sob/shopmanual.io/docs/jeep_lj/05-control-interfaces/02-switchpros-sp1200.md

---
hide:
  - toc
tags:
  - product-details
  - control-interface
  - controller
  - switchpros
---

# SwitchPros SP-1200 (RCR-Force 12) {#switchpros-sp-1200-rcr-force-12}

/// html | div.product-info

**Model:** RCR-Force 12

**Manual:** <https://www.switchpros.com/wp-content/uploads/RCR-force-12-installation-guide-REV-1.9.pdf>

**Power Source:** 150A breaker from [Firewall CONSTANT Bus][firewall-bus] (fed from AUX battery via 250A master CB + 2/0 AWG forward feed)

**Power Wire:** 2 AWG, ~2 ft (Firewall CONSTANT Bus to power module — both at firewall cluster)

**Power Module Location:** Firewall (cabin side, passenger area) — co-located with BODY PDU and Firewall CONSTANT Bus. Module is IP67 / 125°C-rated so wheel well placement is also valid, but firewall mounting minimizes total output wire length since most loads are forward/upper (~58% of outputs).

**Control Panel Location:** Center console top plate, directly behind the [Kilduff shifter][kilduff-shifter] (owner, 2026-09-25). The panel is 4.0 x 3.0 x 0.375 in. It mounts either in a 3.875 x 2.875 in bezel cutout with 0.237 in corners, or on a flat surface on its 6-32 studs.[^rcr12-mount]

**Control Cable:** Not yet ordered. The 5 ft size was picked for a firewall-to-dash run, and the run from the firewall to the console is longer. SwitchPros sells the cable in 5 ft steps from 5 to 50 ft and says to add 6 in for strain relief.[^rcr12-cable] Measure the route before ordering.

**Ground:** 4 AWG to chassis (per manufacturer spec - reference ground only, not load return)

!!! note "Load Ground Path"
    The 4 AWG controller ground is for logic/reference only. Load return current flows through individual output grounds to the [SwitchPros Ground Bus][switchpros-ground-bus] (1/0 AWG to chassis).

**IP Rating:** IP67 (both power module and control panel)

///

## Overview

**Specifications:**

- 150A total capacity on CONSTANT bus
- 17 outputs total:
  - 4 outputs @ 35A (high in-rush circuits)
  - 1 output @ 30A (high in-rush)
  - 11 outputs @ 15A (can be combined for larger loads)
  - 1 low-side driver @ 2A

## Control Panel Layout

| Button | Circuit | Draw | Details | Output Pin(s) |
| :----: | :---: | :--: | :---: | :---: |
| 1 | Roof Lights | 17.6A| 8x BD XL Sport (Linkable, single circuit) | OUTPUT-1 |
| 2 | Ditch Lights |  8A  | 2x BD LP4 Pro (Driving/Combo Pattern) | OUTPUT-2 |
| 3 | Fog Light |  6A  | 1x BD S8 10" (Amber, Wide Cornering) | OUTPUT-3 |
| 4 | Dome Lights |  2A  | 4x KC Cyclone V2 (manual + door-triggered) | OUTPUT-4 |
| 5 | Interior LEDs |  5A  | MLC-RW controller (speaker + footwell RGB) | OUTPUT-5 |
| 6 | Rock Lights |  3A  | 6x KC Cyclone V2 Lights | OUTPUT-6 |
| 7 | Chase Light |  1A  | BD RTL-S 30" (Amber chase mode) | OUTPUT-7 |
| 8 | *Spare* |  - | Freed 2026-09-24: GPS moved to [PMU OUT14][pmu-outputs] (ignition) |  OUTPUT-8 (spare) |
| 9 | *Spare* |  - |  Freed 2026-09-24: front locker moved to a [dash switch][dashboard-controls] | OUTPUT-17 (spare, low-side) |
| 10 | *Spare* |  - | Freed 2026-09-24: rear locker moved to a [dash switch][dashboard-controls] |  OUTPUT-10 (spare) |
| 11 | Compressor | 15A  | ARB Twin Compressor (see [Air System][air-system-arb-compressor-lockers]) | OUTPUT-11 |
| 12 |  Rear Work Lights |  5A  | 2x BD S1 Black (Above License Plate) | OUTPUT-12 |

**Notes:**

- **Button 4:** Dome lights have dual control - Button 4 OR the rear-seat switch via TRIGGER-1
  - Rear-seat switch (latching, closes to ground) → TRIGGER-1 → OUTPUT-4
  - Either one turns the dome lights on. There are no door switches: the Jeep has none, and it runs half doors or no doors (owner, 2026-09-24).
- **Button 7:** RTL-S amber chase function only - brake/running/work functions powered separately
- **Button 11:** OUTPUT-11 provides control signal to ARB compressor (main power is separate: CONSTANT bus → dual 60A fuses → compressor)
- **Cargo Light:** Not assigned to button - controlled by rear rocker switch via TRIGGER-2 → OUTPUT-13 (power source conflict with BODY PDU CB20 — see {{ tbd(147) }})
- Total lighting draw if all on simultaneously: 43.6A (within 150A capacity)

## Wiring Pinout

### 20-Pin Harness Connector

| Pin | Label | Color | Gauge  |  Max Load | Assigned Circuit | Load | Notes |
| :-: | :---: | :---: | :----: | :---: | --- | :--: | :---: |
|  1  | OUTPUT-5  | GREEN | 14 AWG | 15A | Interior LEDs (MLC-RW controller)  |  5A  | |
|  2  | OUTPUT-6  | BLUE | 14 AWG | 15A | Rock Lights |  3A  | |
|  3  | IGNITION  | LT BLUE | - | - | Connect to ignition signal |  - | For auto-off features |
|  4  |  LIGHTS | WHITE | - | - | PMU Out 12 parking/tail circuit (tap at firewall) |  - | Parking-light sense — see [DRL & Parking][drl-parking] |
|  5  | OUTPUT-7  | PURPLE | 14 AWG | 15A | Chase Light (amber) |  1A  | RTL-S amber chase function only |
|  6  | OUTPUT-8  | GREY | 14 AWG | 15A | SPARE |  - | GPS moved to PMU OUT14 (2026-09-24) |
|  7  | TRIGGER-1 | PINK | - | - | Rear-seat dome switch (Blue Sea 4160) |  - | Active low; triggers OUTPUT-4 (dome lights)  |
|  8  | TRIGGER-2 | PINK | - | - | Rear cargo rocker switch |  - | Triggers OUTPUT-13 (cargo light) |
|  9  | OUTPUT-9  | WHITE | 14 AWG | 30A (2x15A) | SPARE (can combine 9+10) |  - | |
| 10  | OUTPUT-9B | WHITE | 14 AWG | - | SPARE (fused with 9) |  - | |
| 11  | OUTPUT-10 | TAN | 14 AWG | 15A | SPARE |  - | Rear locker moved to a dash switch (2026-09-24) |
| 12  | OUTPUT-11 | BROWN | 14 AWG | 15A | Compressor control | 15A  | Control signal to compressor |
| 13  | OUTPUT-12 | RED | 14 AWG | 15A | Rear Work Lights |  5A  | |
| 14  |  GROUND | BLACK | - | - | Direct to battery negative |  - | Critical - direct connection |
| 15  | OUTPUT-13 | ORANGE | 14 AWG | 15A | Cargo Light |  5A  | Triggered by rear rocker switch (TRIGGER-2) |
| 16  | OUTPUT-14 | YELLOW | 14 AWG | 15A | SPARE |  - | |
| 17  | TRIGGER-3 | PINK | - | - | ARB pressure switch |  - | Auto compressor control |
| 18  | OUTPUT-17 |  LT GREEN | - | 2A | SPARE (low-side) |  - | Front locker moved to a dash switch (2026-09-24) |
| 19  | OUTPUT-15 | GREEN/BLACK | 14 AWG | 15A | SPARE |  - | |
| 20  | OUTPUT-16 | BLUE/BLACK  | 14 AWG | 15A | SPARE |  - | |

### 4-Pin Harness (High Current Outputs)

| Pin |  Label | Color  | Gauge | Max Load | Assigned Circuit | Load | Notes |
| :-: | :---: | :----: | :---: | :---: | --- | :--: | :---: |
|  1  | OUTPUT-1 | BROWN  | 10AWG | 35A | Roof Lights (8x) | 17.6A| |
|  2  | OUTPUT-2 |  RED | 10AWG | 35A | Ditch Lights |  8A  | |
|  3  | OUTPUT-3 | ORANGE | 10AWG | 35A | Fog Light |  6A  | |
|  4  | OUTPUT-4 | YELLOW | 10AWG | 35A | Dome Lights |  2A  | |

## Power and Ground Connections

See [AUX Battery Distribution][aux-battery] for source battery and [Firewall CONSTANT Bus][firewall-bus] for downstream distribution.

- **Power:** AUX battery+ → 250A master CB → 2/0 AWG forward (~13 ft) → Firewall CONSTANT Bus → 150A CB → SwitchPros power module
- **Ground (logic reference):** 4 AWG wire from SwitchPros power module → chassis ground at firewall (short run, per manufacturer spec)
- **Load returns:** Each output's ground wire returns to the [SwitchPros Ground Bus][switchpros-ground-bus] (Blue Sea 2105 MaxiBus), co-located with the power module at the firewall

## Trigger Input Assignments

### TRIGGER-1: Rear-Seat Switch → Dome Lights

**Switch Type:** Blue Sea 4160 latching push button, used as a signal switch. It closes TRIGGER-1 to ground and carries no lamp current.

**Why not door switches:** the Jeep has no door switches and runs half doors or no doors (owner, 2026-09-24).

**Wiring:**

```text
Rear-seat switch (latching, SPST) → TRIGGER-1 (Pin 7, PINK)
Other side of switch → chassis ground
```

**Wire Routing:** Rear-seat switch location ({{ tbd(77) }}) → cabin → firewall SwitchPros. 18 AWG (signal only).

**Configuration:**

- Set TRIGGER-1 to active low in the app. The RCR-Force 12 triggers can be set to active high or active low.[^rcr12-trigger]
- Program TRIGGER-1 → OUTPUT-4. Button 4 still switches OUTPUT-4 by hand.

This replaces the parallel, CONSTANT-fed override that would have backfed OUTPUT-4. See [Dome Lights][dome-lights].

### TRIGGER-2: Rear Rocker Switch → Cargo Light

Physical rocker switch mounted in rear cargo area.

**Wiring:**

```text
Rear Cargo Rocker Switch (SPST) → TRIGGER-2 (Pin 8, PINK)
```

**Configuration:**

- Program TRIGGER-2 → OUTPUT-13 (cargo light)
- Switch type: SPST rocker or toggle switch

### TRIGGER-3: Air Pressure Switch → Auto Compressor Control

ARB air tank pressure switch automatically activates compressor to maintain tank pressure between 135-150 PSI.

**Wiring:**

```text
ARB Pressure Switch (180901) → TRIGGER-3 (Pin 17, PINK)
```

**Configuration:**

Program TRIGGER-3 to activate compressor when tank pressure drops below 135 PSI:

**SwitchPros Logic:**

- **TRIGGER-3 OR Button 11 → OUTPUT-11 (compressor)**
- When tank pressure < 135 PSI: TRIGGER-3 closes → OUTPUT-11 activates → compressor runs
- When tank pressure = 150 PSI: TRIGGER-3 opens → OUTPUT-11 deactivates → compressor stops
- Manual override: Button 11 can force compressor on regardless of tank pressure

**Signal Source:**

- ARB Pressure Switch model 180901 (cut-in: 135 PSI, cut-out: 150 PSI)
- Mounted on air manifold under passenger seat
- Low current signal wire (18 AWG from manifold under passenger seat to SwitchPros TRIGGER-3 at firewall — short run)

**Related Documentation:**

- See [Air System][air-system-arb-compressor-lockers] for complete ARB compressor, tank, and pressure switch specifications

## Outstanding Items

{{ tbds() }}

## Build Tasks

Check-off items only. Pin assignments and wire gauges live in the
[Wiring Pinout](#wiring-pinout) section above; controller mounting, power feed,
and ground bus install are tracked in the [Power Systems Checklist][power-checklist].

**Triggers & Programming:**

- [ ] Confirm ignition signal → SwitchPros Pin 3 (IGNITION)
- [x] ~~Determine parking-lights signal source for Pin 4 (LIGHTS)~~ → **Resolved 2026-09-22:** PMU Out 12 parking/tail circuit, tapped at the firewall
- [ ] Measure the control cable route (power module on the firewall to the console) and order the cable
- [ ] Install rear-seat dome switch → TRIGGER-1 (active low)
- [ ] Program Button 4: OUTPUT-4 OR TRIGGER-1 → dome lights
- [ ] Install rear cargo rocker switch → TRIGGER-2 (determine tailgate-accessible location)
- [ ] Program TRIGGER-2 → OUTPUT-13 (cargo light)
- [ ] Confirm cargo light wiring (OUTPUT-13) — power-source conflict pending {{ tbd(147) }}
- [ ] Confirm ARB pressure switch → TRIGGER-3
- [ ] Program TRIGGER-3 OR Button 11 → OUTPUT-11 (compressor auto/manual)
- [ ] Test automatic pressure control (compressor on/off at setpoints)
- [ ] Assign spare outputs: OUTPUT-8, 9, 10, 14, 15, 16 and low-side OUTPUT-17 (buttons 8, 9, 10 are free)

## Related Documentation

- [Control Interfaces Overview][control-interfaces-overview] - Main control interfaces overview
- [Offroad Lighting][offroad-auxiliary-lighting] - Complete wiring details for all lighting circuits controlled by SwitchPros
- [Air System][air-system-arb-compressor-lockers] - ARB compressor wiring details (the lockers now run from [dash switches][dashboard-controls])
- [AUX Battery Distribution][aux-battery] - Power feed specifications for SwitchPros

[aux-battery]: ../01-power-systems/03-aux-battery-distribution/index.md
[firewall-bus]: ../01-power-systems/03-aux-battery-distribution/02-constant-bus.md
[air-system-arb-compressor-lockers]: ../08-exterior-systems/02-air-compressor.md
[control-interfaces-overview]: 01-overview.md
[offroad-auxiliary-lighting]: ../04-offroad-lighting/index.md
[switchpros-ground-bus]: ../01-power-systems/05-grounding/03-switchpros-ground-bus.md
[power-checklist]: ../09-installation/01-power-systems-checklist.md
[drl-parking]: ../03-lighting-systems/05-drl-parking.md
[pmu-outputs]: ../01-power-systems/04-pmu/03-pmu-outputs.md
[dashboard-controls]: 05-dashboard-controls.md
[dome-lights]: ../03-lighting-systems/06-dome-lights.md
[kilduff-shifter]: ../10-drivetrain/01-transmission.md#shifter

[^rcr12-trigger]: SwitchPros RCR-Force 12 installation guide (Rev 1.9), pp. 4 and 7: trigger inputs "can be programmed to trigger on an active high (>4.5V) or active low" signal. <https://www.switchpros.com/wp-content/uploads/RCR-force-12-installation-guide-REV-1.9.pdf> (accessed 2026-09-24).
[^rcr12-mount]: SwitchPros RCR-Force 12 installation guide (Rev 1.9), p. 9 (flat-surface mount on the 6-32 studs, or a 3.875" x 2.875" bezel opening with a 0.237" corner radius) and p. 14 (switch panel size: width 3.0", length 4.0", height 0.375"). <https://www.switchpros.com/wp-content/uploads/RCR-force-12-installation-guide-REV-1.9.pdf> (accessed 2026-09-25).
[^rcr12-cable]: SwitchPros, "RCR-Force 12 Twelve Switch Remote Panel System" store page: cable lengths 5' to 50' in 5' steps, "add a 6 inch allowance for strain relief". <https://store.switchpros.com/rcr-force-12-twelve-switch-remote-panel-system/> (accessed 2026-09-25).
