sob/shopmanual.io/docs/jeep_lj/01-power-systems/STANDARDS-EXCEPTIONS.md

# 1.9 Standards Exceptions & Design Decisions {#standards-exceptions}

This document tracks intentional deviations from general electrical standards where manufacturer specifications, automotive practice, or engineering analysis support alternative approaches.

**Purpose:** Prevent future reviews (AI or human) from flagging intentional design decisions as oversights or errors.

---

## Winch Circuit - No External Overcurrent Protection

**Component:** WARN ZEON 10-S Winch

**Decision:** No external circuit breaker or fuse

**Standards Context:** ABYC E-11 (marine) would require CB, SAE J1128 (automotive) defers to manufacturer

### Manufacturer Specification

**WARN Installation Manual explicitly states:** "No external fuse or circuit breaker required"

- Winch includes integrated thermal protection
- Designed for direct battery connection
- Contactor provides disconnect capability

**Product Page:** [WARN ZEON 10-S][warn-product]

**Installation Manual:** [WARN Installation Guide][warn-manual]

### Winch Engineering Analysis

**Load Characteristics:**

- Typical: 250A continuous during recovery
- Peak: 409A brief (winch stall or heavy load)
- Duration: 10-30 seconds typical, 60 seconds maximum
- Duty Cycle: Brief intermittent use (not continuous)

**Wire Sizing:**

- Wire: 1/0 AWG copper (325A continuous rating @ 60°C)
- Distance: 13 ft one-way (26 ft total circuit)
- Voltage drop @ 250A: 5.32% (0.638V) - acceptable for brief accessory loads
- Voltage drop @ 409A: 8.70% (1.044V) - acceptable for brief peak loads

**Protection Mechanisms:**

1. **Internal Thermal Cutoff**
   - Winch motor has integrated thermal protection
   - Trips before windings reach damage temperature
   - Automatic reset when motor cools

2. **Contactor Disconnect**
   - Isolates winch when not in use
   - Prevents parasitic drain
   - Manual control provides emergency stop

3. **Cable Self-Protection**
   - 1/0 AWG fuses open at ~800A+ (thermal runaway)
   - Well above 409A operating peak
   - Adequate for brief loads per SAE J1128

4. **Manual Battery Disconnect**
   - Master disconnect at AUX battery terminal
   - Emergency shutoff capability
   - Maintenance safety

### Winch Standards Comparison

**Marine (ABYC E-11)** would require a 400A circuit breaker for all loads — **this is not a marine application**, so SAE J1128 (automotive) applies instead, deferring to the manufacturer spec above.

### Winch Fault Scenarios Covered

**Motor Stall (Extended Load):**

- Internal thermal cutoff trips within 60-90 seconds
- Prevents motor damage and fire hazard
- Automatic protection without user intervention

**Cable Short to Chassis:**

- 1/0 AWG cable acts as self-fusing element
- Fault current >800A required to fuse cable open
- Short circuit current path through battery ground and chassis
- Adequate protection for brief fault duration

**Contactor Weld (Stuck Closed):**

- Manual battery disconnect provides emergency stop
- Winch will run until battery depletes or thermal cutoff trips
- User can isolate at battery terminal

**Normal Operating Conditions:**

- 250-409A loads are within winch design parameters
- Cable sizing adequate per voltage drop analysis
- No fire hazard during normal recovery operations

### Winch Review Guidance

**This is NOT an oversight or safety issue** — see Manufacturer Specification, Engineering Analysis, and Standards Comparison above. **Do NOT flag as requiring correction in future reviews.**

**Documentation References:**

- [AUX Battery Distribution][aux-battery-distribution] - Winch connection details (line 37-75)
- [Recovery Systems][recovery-systems] - Complete winch specifications
- [Wire Distance Reference][wire-distance] - Winch cable routing distance

---

## Starter Circuit - No External Circuit Breaker

**Component:** Cummins R2.8 Starter Motor (factory unit shipped with the crate engine)

**Decision:** No external circuit breaker (cable sizing as protection)

**Note:** Timer relay or slow-blow CB could be added for stuck solenoid protection (optional enhancement)

### Starter Industry Standard

**Automotive Practice:**

- Starter circuits typically use cable sizing as protection
- Brief cranking duration (2-5 seconds) does not require CB
- Factory vehicles rarely include starter circuit breakers

**Cummins R2.8:**

- Starter current: 400-600A peak during cranking
- Duration: 2-5 seconds normal cranking
- No external CB specified in installation manual

### Starter Engineering Analysis

**Load Characteristics:**

- Peak: 400-600A during cranking
- Duration: 2-5 seconds typical, 10 seconds maximum recommended
- Duty Cycle: Brief intermittent (engine start only)

**Wire Sizing:**

- Wire: 2/0 AWG copper (375A continuous rating @ 60°C)
- Distance: 6 ft one-way (12 ft total circuit)
- Voltage drop @ 400A: 3.75% (0.450V) - adequate for brief cranking
- Voltage drop @ 600A: 5.61% (0.673V) - adequate for brief cranking

**Protection Strategy:**

1. **Cable Self-Protection (Brief Loads)**
   - 2/0 AWG adequate for 400-600A brief peaks
   - Thermal time constant >> cranking duration
   - No fire hazard during normal cranking

2. **Brake + START Button + P/N Interlock**
   - Prevents starter engagement unless brake pressed, START button held, and shifter in P or N
   - Triple gate eliminates accidental cranking and in-gear cranking

3. **Two-Stage Relay Control**
   - Cole Hersee 24213 solenoid controls high current
   - Low-current control circuit provides isolation

### Potential Fault Scenario: Stuck Solenoid

**Risk:**

- Starter solenoid welds closed or jams
- 400-600A sustained until battery depletes
- Cable heating, potential fire hazard

**Mitigation Options:**

#### Option 1: Timer Relay (Recommended)

- Install 10-second timer in Cole Hersee control circuit
- Cuts power after 10 seconds continuous cranking
- Prevents starter damage and cable overheating
- Lower cost than 500A circuit breaker
- **Status:** Recommended enhancement, not critical requirement

#### Option 2: 500A Slow-Blow Circuit Breaker

- Allows brief 600A cranking peaks
- Trips on sustained high current
- Mechanical Products Series 17 available
- **Status:** Alternative to timer relay

#### Option 3: Current Design (Cable Protection Only)

- Adequate for brief normal cranking ✓
- Relies on user awareness for stuck solenoid
- Manual battery disconnect available
- **Status:** Acceptable per automotive practice, enhancement recommended

### Starter Standards Comparison

**Marine (ABYC E-11)** would require a circuit breaker or fuse — **this is not a marine application**, so SAE J1128 (automotive) applies instead, per the practice and analysis above.

### Starter Review Guidance

**Current design (no CB) is acceptable per automotive standards — do NOT flag as a critical safety issue.** Timer relay remains a recommended (not critical) enhancement; see Option 1 above.

**Documentation References:**

- [Starter System][starter-system] - Complete starter specifications and wiring (line 1-125)
- [START Battery Distribution][starter-battery-distribution] - Starter power connection (line 37)

---

## Grid Heater - Direct Battery Connection (No CB)

**Component:** Cummins R2.8 Grid Heater Relay (Part# 5467024)

**Decision:** Direct battery connection with fusible link (no circuit breaker)

### Grid Heater Manufacturer Specification

**Cummins Installation:**

- ECM controls grid heater relay directly
- High current (40-80A) for brief duration (3-5 seconds)
- Direct battery connection specified
- Fusible link protection integrated

### Grid Heater Engineering Analysis

**Load Characteristics:**

- Current: 40-80A during cold start aid
- Duration: 3-5 seconds (brief pulse)
- Duty Cycle: Only during cold starts (<50°F ambient)
- Frequency: Infrequent (cold weather only)

**Protection Strategy:**

- Integrated fusible link in relay assembly
- ECM manages duty cycle and temperature thresholds
- Brief duration eliminates thermal concerns
- Direct connection minimizes voltage drop for effective heating

### Grid Heater Review Guidance

**This is intentional per manufacturer specifications** — see Engineering Analysis above. **Do NOT flag as requiring circuit breaker.**

**Documentation References:**

- [Grid Heater System][grid-heater] - Complete grid heater specifications

---

## Alternator Output - No Circuit Breaker

**Component:** Premier Power Welder HO-C28 270A Alternator

**Decision:** No circuit breaker between alternator and battery

### Alternator Industry Standard

**All automotive alternators connect directly to battery without circuit breaker:**

- Factory vehicle practice: No CB on alternator output
- Alternator has internal voltage regulation
- Charging circuit protected by battery capacity and cable sizing

### Alternator Engineering Analysis

**Why No Circuit Breaker Required:**

1. **Alternator Self-Limiting**
   - Maximum output: 270A (design limit)
   - Cannot exceed rated output regardless of load
   - Internal voltage regulator prevents overcharge

2. **Cable Sizing**
   - Wire: 2/0 AWG (375A continuous rating)
   - Adequate for 270A continuous output
   - No thermal concerns at rated load

3. **Battery Acts as Buffer**
   - Absorbs brief load spikes
   - Prevents alternator overload
   - Natural load smoothing

### Alternator Review Guidance

**This is standard automotive practice** — see Industry Standard and Engineering Analysis above. **Do NOT flag as missing protection.**

**Documentation References:**

- [Alternator][alternator] - Alternator specifications and output connection

---

## BCDC Charging Input - No Dedicated Circuit Breaker

**Component:** RedArc BCDC Alpha 50 DC-DC Charger

**Decision:** 80A circuit breaker at START battery terminal (not at BCDC)

### BCDC Manufacturer Specification

**RedArc Installation:**

- Circuit breaker required within 7" of battery positive
- No requirement for CB at BCDC input
- 80A CB adequate for 50A charging current + inrush

### BCDC Engineering Analysis

**Protection Location:**

- CB at battery terminal (compliant with 7" requirement) ✓
- Protects entire cable run from battery to BCDC ✓
- No additional CB needed at BCDC end

**Load Characteristics:**

- Normal: 50A DC-DC charging
- Peak: 50-55A (manufacturer spec)
- 80A CB sized at 145-160% of max load (appropriate margin)

### BCDC Review Guidance

**Circuit breaker at the battery terminal is the correct protection point** — see Engineering Analysis above. **Do NOT flag as missing protection at BCDC.**

**Documentation References:**

- [BCDC Alpha 50][bcdc] - BCDC installation and protection requirements
- [START Battery Circuit Breakers][starter-cbs] - 80A CB specification

---

## START+ Forward Distribution Bus - Bus Bar Between Battery and Loads

**Components:** START+ Forward Distribution Bus (engine bay) feeding the relocated radiator fan, iBooster, and TCU

**Decision:** A single 100A master-protected 2 AWG feed runs from the START battery to an engine-bay busbar that fans out to three load breakers — a deliberate departure from the START-side "direct lugs, no bus bar between battery and loads" principle.

### Engineering Rationale

- The radiator fan, iBooster, and TCU were moved off the PMU and all sit forward (engine bay / transmission), while the START battery is in the rear wheel well.
- Three independent feeds would mean three long rear-to-front cables and ~9 stacked lugs on the battery post (impractical, hard to service).
- A single master feed + forward busbar mirrors the proven AUX-side two-stage architecture (250A master → firewall CONSTANT bus), placing each load's breaker near its load.
- The intermediate bus is a passive bar; the feed is protected by a 100A master breaker within 7" of the battery (the cable is never unprotected), with selective coordination to the downstream load breakers.

### Review Guidance

**This is intentional.** Do NOT flag the START+ Forward Distribution Bus as violating the "no bus bar between battery and loads" rule — it is the same accepted tradeoff as the AUX CONSTANT bus, chosen to relocate three critical loads off the PMU. See {{ tbd(135) }} for final busbar/breaker selection.

**Documentation References:**

- [START Battery Distribution][starter-battery-distribution] - Forward bus feed and load table
- [START Battery Circuit Breakers][starter-cbs] - Master + load breakers

---

## SwitchPros & SafetyHub - CB Sized for Device Capacity

**Components:** SwitchPros RCR-Force 12, Blue Sea SafetyHub 150

**Decision:** 150A circuit breakers protecting 2 AWG wire (130A @ 20°C)

**Apparent Issue:** CB rating (150A) exceeds wire continuous ampacity (130A) by 15%

### Engineering Analysis

**Why This Is Safe:**

The CB is sized for _device capacity_, not actual load. Actual loads are well within wire rating:

| Device | Device Max | Actual Load | Wire Rating | Load % of Wire |
| :--- | :--- | :--- | :--- | :--- |
| SwitchPros | 150A | ~48A | 130A | 37% |
| SafetyHub  | 150A | 100A | 130A | 77% |

**SwitchPros Actual Load Breakdown:**

- Roof lights: 18A (8x XL Sport @ 2.2A each)
- Auxiliary lights: 26A (ditch 8A, fog 6A, work 5A, rock 3A, dome 2A, chase 1A, rear 5A)
- Lockers: 4A
- **Total: ~48A** (32% of CB rating)

**SafetyHub Actual Load Breakdown:**

- ARB Compressor: 90A (2x 45A motors)
- Winch trigger: 10A
- **Total: 100A** (67% of CB rating)

### Protection Strategy

**Normal Operation:**

- Wire operates at 37-77% of its ampacity
- No thermal stress, adequate safety margin
- Wire temperature remains well below insulation rating

**Fault Condition (Short Circuit):**

- Fault current exceeds CB rating → CB trips
- Brief overload duration (milliseconds to seconds) insufficient to damage wire
- 2 AWG thermal mass absorbs brief fault current safely

**CB Trip Curve Analysis:**

- Mechanical Products Series 17 trips at 135% of rating within 30 seconds
- At 150A × 135% = 202A, CB trips before wire reaches damage temperature
- Short circuit currents (500A+) trip CB nearly instantaneously

### Wire Sizing Rationale

**Why 2 AWG (not 1/0 AWG):**

1. **Actual load headroom:** 82-100A loads have 30-48A margin to wire rating
2. **Consistency:** All CONSTANT bus outputs use 2 AWG for standardization
3. **Future flexibility:** 130A wire supports load growth within device capacity
4. **Cost/weight:** 1/0 AWG unnecessary for actual loads

**Why 150A CB (not 125A):**

1. **Device protection:** Matches SwitchPros and SafetyHub rated capacity
2. **Inrush tolerance:** Lighting loads have brief inrush spikes
3. **Future headroom:** Allows adding loads up to device capacity

### Standards Context

**ABYC E-11 (Marine):**

- Requires CB ≤ wire ampacity for continuous loads
- **However:** Actual loads are not continuous at full capacity
- SwitchPros lighting loads are intermittent (not 24/7 operation)
- SafetyHub ARB compressor runs only during airing up (minutes, not hours)

**SAE J1128 (Automotive):**

- Wire sizing based on actual load, not theoretical maximum
- CB sizing considers duty cycle and thermal time constants
- Brief overloads acceptable if within wire thermal limits

### Review Guidance

**This is NOT a safety issue** — the apparent CB > wire mismatch is intentional; see Engineering Analysis, Wire Sizing Rationale, and Standards Context above. **Do NOT flag as requiring wire upgrade or CB downgrade.**

**Documentation References:**

- [AUX Battery Circuit Breakers][aux-cbs] - CB specifications
- [CONSTANT Bus Bar][constant-bus] - Wire specifications
- [SwitchPros][switchpros] - Load assignments and totals
- [SafetyHub][safetyhub] - Circuit assignments and loads

---

## Summary of Intentional Design Decisions

**All decisions documented above are intentional and based on:**

1. **Manufacturer Specifications** - Following OEM installation requirements
2. **Automotive Standards (SAE J1128)** - Primary standard for automotive electrical systems
3. **Industry Practice** - Factory vehicle precedents and proven approaches
4. **Engineering Analysis** - Load characteristics, wire sizing, fault scenarios

**These are NOT oversights, errors, or safety issues.**

**Marine standards (ABYC E-11) are referenced selectively:**

- Applied to: Dual battery architecture, accessory circuits, grounding
- **NOT applied to:** Starter, alternator, winch, grid heater (automotive components)

---

## Breaker-vs-Wire Preference (2026-09-22)

Owner rule: **keep the smaller wire and drop the breaker to it.** When a review finds a breaker above its conductor's ampacity, the fix is a lower-rated breaker at or below the wire rating, not a heavier cable — the build is already carrying a lot of copper. Applied so far:

| Circuit | Was | Now | Wire it protects |
| :--- | :-- | :-- | :--- |
| START+ Forward Distribution Bus master | 150A | 100A | 2 AWG (110A @ 60°C) |
| AUX forward feed to Firewall CONSTANT Bus | 300A | 250A | 2/0 AWG (~265A @ 60°C); matches the 2105 bus rating |
| JL Audio MV800/8i amp feed | 100A | 80A | 4 AWG (95A @ 20°C); equals the amp's recommended fuse |

Manufacturer-specified breakers (SwitchPros 150A, SafetyHub 150A) keep their exception above.

## Review Checklist for Future Analysis

Before flagging as issues, verify these intentional design choices:

- [ ] **Winch:** No external CB per WARN manufacturer spec ✓
- [ ] **Starter:** Direct battery connection, cable sizing as protection (timer relay optional enhancement)
- [ ] **Grid Heater:** Direct battery connection with fusible link (brief high current)
- [ ] **Alternator:** No CB on output (standard automotive practice)
- [ ] **BCDC:** CB at battery terminal (no CB at BCDC end required)
- [ ] **START+ Forward Bus:** 100A master + forward busbar between battery and fan/iBooster/TCU (intentional, mirrors AUX CONSTANT bus)
- [ ] **SwitchPros/SafetyHub:** 150A CB with 2 AWG wire (actual loads 82-100A, within 130A wire rating)

**If any of these are flagged as "missing protection" or "safety issues" in future reviews, refer to this document for complete justification.**

---

[warn-product]: https://www.warn.com/products/zeon-10-s-89611
[warn-manual]: https://www.warn.com/products/zeon-10-s-89611
[aux-battery-distribution]: 03-aux-battery-distribution/index.md
[recovery-systems]: ../08-exterior-systems/01-winch.md
[wire-distance]: 01-power-generation/05-wire-distance-reference.md
[starter-system]: ../02-engine-systems/01-starter.md
[starter-battery-distribution]: 02-starter-battery-distribution/index.md
[grid-heater]: ../02-engine-systems/07-grid-heater.md
[alternator]: 01-power-generation/02-alternator.md
[bcdc]: 01-power-generation/03-bcdc.md
[starter-cbs]: 02-starter-battery-distribution/01-circuit-breakers.md
[aux-cbs]: 03-aux-battery-distribution/01-circuit-breakers.md
[constant-bus]: 03-aux-battery-distribution/02-constant-bus.md
[switchpros]: ../05-control-interfaces/02-switchpros-sp1200.md
[safetyhub]: 03-aux-battery-distribution/04-safetyhub.md
