sob/shopmanual.io/docs/jeep_lj/02-engine-systems/01-starter.md

---
hide:
  - toc
tags:
  - product-details
  - engine-systems
  - starter
---

# 2.1 Starter System {#starter-system-cummins-r28}

/// html | div.product-info
**Type:** 12V Diesel Starter Motor

**Model:** Cummins factory starter — shipped mounted on the R2.8 crate engine[^kit-starter]

**Status:** In hand (owner decision 2026-09-22: keep the factory unit)

**Manufacturer:** Cummins (supplier unit)

**Voltage:** 12V

**Mounting:** Engine block (as shipped)

**Power Source:** START battery+ direct connection (2/0 AWG)

**Replacement reference (not purchased):** [DB Electrical 410-52442][db-starter] — aftermarket cross-reference to Cummins 4996706 / Denso 428000-7090; useful only if the factory unit ever needs replacing.

///

[^kit-starter]: Cummins Repower R2.8 Installation Guide (Bulletin 5504137), §1 "Starter", p. 1-36: "The engine kit includes an engine mounted 12 volt starting motor." Local copy: `resources/cummins-r2.8-installation-guide.pdf`.

## System Configuration

**Control Method:** Two-stage relay system

**Main Power Source:** START battery+ direct connection (see [START Battery Distribution][starter-battery] for wire specs)

**Control Solenoid:** Cole Hersee 24213 (200A continuous-duty)[^ch-24213]

**Safety Interlock:** The crank signal (60A PURPLE START) comes solely from the PBS-I keyless module, which owns RFID authorization, the brake interlock, ACC/IGN/START sequencing, and the cold-start WAIT-to-Start lamp procedure — see [Keyless Ignition][keyless-ignition]. (An automatic crank lockout was evaluated and deferred — see the [WAIT-to-Start Lockout Design Note][wait-lockout-note].)

**Battery Requirement:** 800 CCA minimum (Odyssey PC1500 provides 850 CCA)

## Wiring

| Circuit | Source | Destination | Wire Gauge | Current  | Notes |
| :--- | :--- | :--- | :--- | :--- | :--- |
| Main Power | START battery+ | Starter solenoid battery post | 2/0 AWG | 400-600A | See [START Battery Distribution][starter-battery] for wire specs |
| Solenoid Power Tap | START battery post | Cole Hersee 24213 input | 10 AWG | 30-75A | ~2 ft |
| Start Signal | PBS-I PURPLE START output | Firewall Pin 15 → Cole Hersee coil+ | 16 AWG  | ~0.69A | PBS-I output rated 60A but only Cole Hersee coil downstream[^ch-24213] |
| Solenoid Coil Ground  | Cole Hersee 24213 coil- | Engine bay ground bus | 16 AWG | ~0.69A | ~3 ft |
| Solenoid Output | Cole Hersee 24213 output | Starter solenoid switch post | 10 AWG | 30-75A | ~2 ft |
| Ground Return | Starter case | Engine block → START battery- | 2/0 AWG | 400-600A | Via engine bay ground bus |

See [Keyless Ignition][keyless-ignition] for PBS-I power and brake input wiring.

## Control Flow

```text
PBS-I asserts PURPLE START  (fob auth + brake + sequence: see Keyless Ignition)
            ↓
PURPLE START → Firewall Pin 15 → Cole Hersee 24213 coil → Ground
            ↓
Cole Hersee main contacts close
            ↓
START battery → Cole Hersee output → Starter switch post → Bendix engages → cranks
            ↓
Engine starts → button released → Cole Hersee de-energizes → Bendix retracts
```

## Starter Motor Terminals

**Battery Post (M8 x 1.25 thread, qty 2):**

- Main power from START battery (2/0 AWG)
- Power tap for control solenoid (10 AWG)

**Switch Post (6.3mm flat male push-on):**

- Trigger from Cole Hersee 24213 output (10 AWG, 30-75A)

**Ground:**

- Via starter mounting bolts to engine block

## Cole Hersee 24213 Solenoid

**Specifications:**

- Rating: 200A continuous duty[^ch-24213]
- Coil Voltage: 12V DC
- Coil Draw: ~0.69A (17.5 Ω coil @ 12V)[^ch-24213]
- Mounting: Firewall (engine bay side)

**Terminals:**[^ch-24213]

- Large Stud 1 (Input): 5/16"-24 copper power stud; from START battery post (10 AWG)
- Large Stud 2 (Output): 5/16"-24 copper power stud; to starter switch post (10 AWG; starter post is 6.3mm push-on)
- Small Stud 1 (Coil+): #10-32 steel stud; from Firewall Pin 15 (16 AWG, PBS-I PURPLE START)
- Small Stud 2 (Coil-): #10-32 steel stud; to engine bay ground bus (16-18 AWG)

[^ch-24213]: Littelfuse (Cole Hersee) 24213 continuous-duty SPST solenoid, [product page](https://www.littelfuse.com/products/relays-contactors-transformers/solenoids-relays/standard-high-current-relays/continuous-duty-spst/24213) / DigiKey #6347082. Rated **200A continuous** with two 5/16"-24 copper power studs + two #10-32 steel coil studs; coil ~0.69A @ 12V (17.5 Ω). Corrects the earlier unsourced "85A / M8 / 6.3mm-push-on" figures (validated 2026-05-30). 200A is comfortably oversized for the ~10A starter-trigger path.

## Outstanding Items

{{ tbds() }}

## Build Tasks

- [ ] Record the factory starter's part number from its tag (the terminal posts and current figures below were taken from the aftermarket cross-reference; confirm on the unit)

[install-checklist]: ../09-installation/02-engine-systems-checklist.md

## Related Documentation

- [START battery Distribution][starter-battery-distribution] - Main power source
- [Firewall Ingress][firewall-ingress] - Ignition START wire routing
- [Engine Bay Ground Bus][engine-bay-ground-bus] - Ground connections
- [Power Generation][power-generation] - Battery specifications
- [Wire Distance Reference][wire-distance] - Starter to battery routing distances
- [Keyless Ignition][keyless-ignition] - PBS-I sources PURPLE START; cold-start wait via the WAIT-to-Start lamp
- [WAIT-to-Start Lockout Design Note][wait-lockout-note] - Deferred automatic crank-lockout design, preserved for future revival

[db-starter]: https://www.dbelectrical.com/products/starter-for-2-8-cummins-isf2-8-qsb3-9-30-qsb4-5-4996706-428000-7090.html
[starter-battery-distribution]: ../01-power-systems/02-starter-battery-distribution/index.md
[starter-battery]: ../01-power-systems/02-starter-battery-distribution/index.md
[firewall-ingress]: ../01-power-systems/07-wire-routing/02-firewall-ingress.md
[engine-bay-ground-bus]: ../01-power-systems/05-grounding/01-engine-bay-ground-bus.md
[power-generation]: ../01-power-systems/01-power-generation/index.md
[wire-distance]: ../01-power-systems/01-power-generation/05-wire-distance-reference.md
[keyless-ignition]: ../05-control-interfaces/06-keyless-ignition.md
[wait-lockout-note]: wait-to-start-lockout-design-note.md
[tbd-tracker]: ../tbd-tracker.md
