sob/shopmanual.io/docs/jeep_lj/08-exterior-systems/04-rear-air-chuck.md

---
hide:
  - toc
tags:
  - product-details
  - exterior-systems
  - air-system
---

# 8.4 Rear Air Chuck {#rear-air-chuck}

External air access plate mounted in the tailgate area for tire inflation, air tool use, and trail-side air sharing with other vehicles.

/// html | div.product-info

**Type:** Quick-disconnect air chuck plate

**Location:** Tailgate area

**Air Source:** [Air Compressor][air-compressor] via manifold (1/4" air line)

///

## Specifications

| Spec | Value |
| --- | --- |
| Connector Type | Industrial quick-disconnect (1/4" NPT) |
| Working Pressure | 150 PSI (matches tank pressure) |
| Air Line | 1/4" OD nylon tubing from manifold |
| Mounting | Flush-mount plate in tailgate area |

## Air Line Routing

**Route:** Manifold (under passenger seat) → along interior → to tailgate area

- **Line Type:** 1/4" OD nylon tubing (200 PSI rated)
- **Fittings:** Push-to-connect at manifold, NPT fitting at chuck plate
- **Protection:** Route inside vehicle where possible, protect at penetrations

## Outstanding Items

{{ tbds() }}

## Build Tasks

- [ ] Select air chuck plate model/part number
- [ ] Determine exact mounting location in tailgate area
- [ ] Measure air line length from manifold to tailgate
- [ ] Order air chuck plate and fittings

## Related Documentation

- [Air Compressor][air-compressor] - Air source and manifold
- [Air Lockers][air-lockers] - Other air system consumers

[air-compressor]: 02-air-compressor.md
[air-lockers]: 03-air-lockers.md
