sob/shopmanual.io/docs/jeep_lj/04-offroad-lighting/10-reverse-lights.md

---
hide:
  - toc
tags:
  - product-details
  - lighting
  - offroad
  - pmu-controlled
  - baja-designs
---

# 4.10 Reverse Lights {#reverse-lights}

Reverse lights (4,520 lumens combined) that activate automatically via PMU reverse circuit.

/// html | div.product-info
Baja Designs Squadron Sport

**Type:** LED Pod Light

**Model:** Squadron Sport Black - Wide Cornering

**Part Number:** 557805

**Manufacturer:** Baja Designs

**Product Page:** [Squadron Sport Wide Cornering Pair][product-link]

**Quantity:** 2 pods

**Mounting:** Rear armor brackets

**Power Source:** PMU Out 22 (automatic with reverse gear)

///

## Specifications

| Spec | Value |
| :--- | ---: |
| Beam Pattern | Wide Cornering 42° |
| Lens | Clear |
| Output | 2,260 lumens each (4,520 total) |
| Draw | 1.4A each (2.8A total) |
| IP Rating | IP69K |

## Control

**Controller:** PMU Out 22 (automatic with reverse gear)

Wired in parallel with Maxbilt Round Trail Tail WHITE (reverse) and WolfBox camera trigger.

See [Tail/Brake/Reverse Lights][tail-brake-reverse] for PMU reverse circuit details and combined load verification.

## Related Documentation

- [Offroad Lighting Overview][offroad-overview]
- [Tail/Brake/Reverse Lights][tail-brake-reverse] - PMU Out 22 reverse circuit
- [Rear Work Lights][rear-lights] - Separate SwitchPros-controlled rear lights

[offroad-overview]: index.md
[tail-brake-reverse]: ../03-lighting-systems/04-tail-brake-reverse.md
[rear-lights]: 08-rear-lights.md
[product-link]: https://www.bajadesigns.com/products/squadron-sport-led-light-557805.html
