sob/shopmanual.io/docs/jeep_lj/04-offroad-lighting/07-cargo-lights.md

---
hide:
  - toc
tags:
  - product-details
  - lighting
  - offroad
  - baja-designs
---

# 4.7 Cargo Lights {#cargo-lights}

Interior cargo area lighting controlled by physical switch (Baja Designs Zone 7).

/// html | div.product-info
Baja Designs S2 Sport Flush Mount

**Type:** LED Flush Mount Light

**Model:** S2 Sport Black Flush Mount

**Part Number:** 541006

**Manufacturer:** Baja Designs

**Product Page:** [S2 Sport Black Flush Mount][product-link]

**Quantity:** 2 pods

**Mounting:** Flush mount inset on rear wheel well (cargo area)

**Power Source:** BODY PDU (via physical switch)

///

## Specifications

| Spec | Value |
| :--- | ---: |
| Beam Pattern | Work/Scene |
| Lens | Clear |
| Draw | ~2A each (4A total) |

## Control

**Controller:** [Blue Sea 4160 Push Button Switch][switch-link]

**Switch Location:** Top of rear wheel well (accessible from tailgate)

**Wiring:** BODY PDU CB20 (10A) → Switch → Cargo lights → Ground (power-source conflict with OUTPUT-13/TRIGGER-2 open — {{ tbd(147) }})

| Spec | Value |
| :--- | ----: |
| Switch Rating | 10A @ 12V |
| Load | 4A |
| Action | OFF-ON (latching) |
| Mounting Hole | 3/4" (19mm) |

## Related Documentation

- [Offroad Lighting Overview][offroad-overview]
- [BODY PDU][body-pdu] - CB20 power source

[offroad-overview]: index.md
[body-pdu]: ../01-power-systems/03-aux-battery-distribution/03-body-pdu.md
[product-link]: https://www.bajadesigns.com/products/s2-sport-black-flush-mount-led-auxiliary-light-pod/?sku=541006
[switch-link]: https://www.bluesea.com/products/4160/10A_Push_Button_LED_Ring_Switch_OFF-ON_Blue
