sob/shopmanual.io/docs/jeep_lj/04-offroad-lighting/03-roof-lights.md

---
hide:
  - toc
tags:
  - product-details
  - lighting
  - offroad
  - switchpros-controlled
  - baja-designs
---

# 4.3 Roof Lights {#roof-lights}

Primary forward illumination mounted on roof rack (Baja Designs Zone 3 + Zone 4).

/// html | div.product-info
Baja Designs XL Sport Linkable 8-Pod

**Type:** LED Pod Light (Linkable)

**Model:** XL Sport Linkable

**Part Number:** 740006

**Manufacturer:** Baja Designs

**Product Page:** [XL Sport Linkable 8-Pod][product-link]

**Quantity:** 8 pods total

**Harness:** [XL Linkable Wiring Harness 8-Pod][harness-link] (640192)

**Mounting:** [XL Linkable Pre-Load Mount][preload-link] (748002) center + [XL Linkable Brackets][bracket-link] (748000) sides

**Power Source:** SwitchPros OUTPUT-1

///

## Wiring

All 8 pods on single circuit via XL Linkable harness.

**Wire Routing:** Passenger A-pillar from SwitchPros (engine bay) to roof rack.

**Controller:** SwitchPros Button 1 (OUTPUT-1) - 17.6A load on 35A output (50% utilization)

## Specifications

| Spec | Value |
| :--- | ---: |
| Output | 9,000 lumens each |
| Draw | 2.2A each (30.36W) |
| Total Output | 72,000 lumens |
| Total Draw | 17.6A |

See [SwitchPros SP-1200][switchpros-sp-1200] for wiring details.

## Outstanding Items

{{ tbds() }}

## Build Tasks

- [ ] Plan wire routing from SwitchPros to roof rack (passenger A-pillar to roof)
- [ ] Confirm roof rack mounting points for XL Linkable brackets

## Related Documentation

- [Offroad Lighting Overview][offroad-overview]
- [SwitchPros SP-1200][switchpros-sp-1200]

[offroad-overview]: index.md
[switchpros-sp-1200]: ../05-control-interfaces/02-switchpros-sp1200.md
[product-link]: https://www.bajadesigns.com/products/xl-sport-linkable-led-light-bar-universal/?sku=740006
[harness-link]: https://www.bajadesigns.com/products/xl-linkable-wiring-harness-universal/?sku=640192
[preload-link]: https://www.bajadesigns.com/products/xl-linkable-led-light-bar-pre-load-mount/?sku=748002
[bracket-link]: https://www.bajadesigns.com/products/xl-linkable-led-light-bar-brackets/?sku=748000
