sob/shopmanual.io/docs/jeep_lj/04-offroad-lighting/06-rock-lights.md

---
hide:
  - toc
tags:
  - product-details
  - lighting
  - offroad
  - switchpros-controlled
  - kc-hilites
---

# 4.6 Rock Lights {#rock-lights}

Underbody lighting for wheel wells and frame rails (Baja Designs Zone 6).

/// html | div.product-info
KC HiLiTES Cyclone V2

**Type:** LED Rock Light

**Model:** Cyclone V2

**Part Number:** 1352 (single light)

**Manufacturer:** KC HiLiTES

**Product Page:** [Cyclone V2][product-link]

**Quantity:** 6 pods

**Mounting:** 4 in wheel wells (one per corner), 1 front bumper, 1 rear bumper

**Power Source:** SwitchPros OUTPUT-6

///

## Specifications

| Spec | Value |
| :----- | ---: |
| Output | 200 lumens each (1,200 total) |
| Draw | 0.5A each (3A total) |
| Size | 2.4" diameter round |

## Control

**Controller:** SwitchPros Button 6 (OUTPUT-6)

See [SwitchPros SP-1200][switchpros-sp-1200] for wiring details.

**Protection:** Braided sleeving with soldered connections and marine heat shrink.

## Outstanding Items

{{ tbds() }}

## Build Tasks

- [ ] Plan wire routing from SwitchPros to wheel wells and bumpers

## Related Documentation

- [Offroad Lighting Overview][offroad-overview]
- [SwitchPros SP-1200][switchpros-sp-1200]

[offroad-overview]: index.md
[switchpros-sp-1200]: ../05-control-interfaces/02-switchpros-sp1200.md
[product-link]: https://www.kchilites.com/cyclone-v2-cyclone-v2-led-single-light.html?attr_pim_lenscolor=5730
