sob/shopmanual.io/docs/jeep_lj/01-power-systems/02-starter-battery-distribution/index.md

---
hide:
  - toc
---

# 1.2 START battery Distribution (Driver Rear Wheel Well) {#starter-battery-distribution}

/// html | div.product-info
Odyssey PC1500 Battery Terminals
///

## Overview

The START battery (driver rear wheel well) provides power for critical engine and safety systems:

1. **Direct high-current** → Starter (no CB), alternator charging input (no CB)
2. **Circuit breaker protected** → PMU (250A CB), BCDC (80A CB)
3. **[START+ Forward Distribution Bus](#start-forward-bus)** (100A master CB → single feed → engine-bay busbar) → radiator fan (60A), iBooster main (50A), TCU (25A) — relocated off the PMU
4. **Direct low-current** → ECM, grid heater (fusible link protection)

See [Circuit Breakers][circuit-breakers] for complete CB specifications. All CBs mounted in rear wheel well within 7" of battery (code compliant).

!!! info "Single Source of Truth"
This page is the authoritative source for all START battery wire specs (gauge, distance, voltage drop). Component pages reference here. For battery specs see [Section 1.1][batteries]. For ground bus bars see [Section 1.5][grounding].

## START battery Positive Terminal (7 connections)

| Circuit | Destination | Wire Gauge  | Distance | Current  | Voltage Drop | Protection |
| :--- | :--- | :--- | :--- | :--- | :--- | :--- |
| [Alternator][alternator] | Engine bay | 2/0 AWG | 8 ft | 270A | 2.81% @ 60°C | None |
| [Starter][starter] | Engine bay | 2/0 AWG | 6 ft | 400-600A | 1.9-3.9% @ 20°C | None |
| [PMU24][pmu] | Engine bay | 2/0 AWG | ~7 ft | 250A max | 2.4% @ 60°C | 250A CB |
| [START+ Forward Dist Bus](#start-forward-bus) | Engine bay | 2 AWG | ~8 ft | ~108A peak | 1.3% @ 60°C | 100A master CB |
| ECM | Engine bay | Per Cummins | Short | <5A | Negligible | Fusible link |
| [Grid Heater][grid-heater] | Engine bay | Per Cummins | Short | ~80A | Negligible | Fusible link |
| [BCDC Alpha 50][bcdc] | Passenger rear wheel well | 4 AWG | ~6 ft | 50A | 0.94% @ 20°C | 80A CB |

All circuit breakers mounted within 7" of battery (ABYC/NEC compliant). See [Circuit Breakers][circuit-breakers].

## START+ Forward Distribution Bus {#start-forward-bus}

The radiator fan, iBooster, and TCU were relocated off the PMU onto START-direct power. All three sit forward (engine bay / transmission) while the START battery is in the rear wheel well, so — mirroring the [AUX forward-feed architecture][constant-bus] — a **single master-protected feed** runs forward to an engine-bay busbar that fans out to the three loads on short local feeds. This keeps the long rear-to-front run to one heavy cable instead of three, and places each load's breaker near its load.

**Busbar:** Blue Sea 2105 MaxiBus (250A), engine bay, insulated cover — recommended; confirm with {{ tbd(135) }}
**Master feed:** 2 AWG, ~8 ft, 100A CB at battery post (<7") — downsized from 150A so the breaker sits at or below the 2 AWG ampacity (110A @ 60°C)

| Load | Feed (from bus) | Wire Gauge | Distance | Current | Voltage Drop | Breaker |
| :--- | :--- | :--- | :--- | :--- | :--- | :--- |
| [Radiator Fan][radiator-fan] | Radiator shroud | 4 AWG | short | 53A continuous | <1% @ 60°C[^fwd-bus-vdrop] | 60A |
| [iBooster][brake-booster] main | Firewall | 8 AWG | short | 40A peak / 0.25A idle | <0.5%[^fwd-bus-vdrop] | 50A |
| [Turbolamik TCU][transmission] | Transmission | 12 AWG | short | 15A continuous | <0.5%[^fwd-bus-vdrop] | 25A |

The master feed carries the combined load (~68A continuous, ~108A brief peak); voltage drop and breaker sizing are set on that single cable.[^fwd-bus-vdrop] The iBooster's separate ignition **enable** (~5A) is sourced from the [Ignition Signal bus][ignition-signal], not this bus. Fan speed is set by a dedicated fan controller ({{ tbd(134) }}) with its own coolant sensor, independent of the PMU and J1939.

!!! info "Shared forward feed — intentional tradeoff"
    This is the same shared-feed tradeoff the [AUX side][constant-bus] accepts, and is more robust than the loads' former shared dependency on the PMU module. Each load keeps its own breaker. See [Standards Exceptions][standards-exceptions] for the full "no bus bar between battery and loads" exception rationale.

[^fwd-bus-vdrop]: Master feed 2 AWG @ ~108A brief peak (~68A continuous), ~8 ft, 60°C-derated (×1.2) ≈ 1.3% — sized on the combined load. Load feeds are short from the engine-bay bus, so per-load drop is negligible: fan 4 AWG @ 53A, iBooster 8 AWG @ 40A brief, TCU 12 AWG @ 15A. Final master-feed length and breaker selective-coordination pending {{ tbd(136) }} and {{ tbd(135) }}.

## START battery Negative Terminal (6 connections)

| Circuit | Destination | Wire Gauge  | Distance | Current | Voltage Drop  |
| :--- | :--- | :--- | :--- | :--- | :--- |
| [Engine Bay Ground Bus][engine-ground-bus] | Engine bay | 2/0 AWG | ~8 ft | 600A+ peak | <0.1V @ 60°C  |
| ECM | Engine bay | 12 AWG | Short | <5A | Negligible |
| [Grid Heater][grid-heater] | Engine bay | Per Cummins | Short | ~80A | Negligible |
| [AUX Battery][aux-battery] | Passenger rear wheel well | 1/0 AWG | 5-6 ft | 75A max | <0.05V @ 20°C |
| [G1 GMRS Radio][radios] | Roll cage, overhead  | 10 AWG | Measure  | 15A TX | Recheck |
| [STX Intercom][radios] | Dashboard | 10 AWG | ~8 ft | 5A | 0.4% @ 20°C |

Radio grounds direct to battery for RF noise isolation. ECM/grid heater via Cummins harness to isolate from starter spikes.

START− intentionally has no local chassis bond — its chassis reference is the 2/0 AWG run to the [Engine Bay Ground Bus][engine-ground-bus] (the rear frame chassis bond lives on the AUX− side). The 6 connections above are the complete, final set; an earlier "7 connections" count was an error.

## Related Documentation

- [Power Generation][power-gen] - Battery and alternator specifications
- [Circuit Breakers][circuit-breakers] - Complete CB specifications
- [Grounding Architecture][grounding] - Ground bus bars
- [PMU24][pmu] - Power management unit
- [BCDC Alpha 50][bcdc] - DC-DC charger to AUX battery
- [Starter System][starter] - Starter specifications
- [Alternator][alternator] - Charging system
- [AUX battery Distribution][aux-battery] - Aux/accessory battery system

[pmu]: ../04-pmu/index.md
[bcdc]: ../01-power-generation/03-bcdc.md
[batteries]: ../01-power-generation/01-batteries.md
[grid-heater]: ../../02-engine-systems/07-grid-heater.md
[grounding]: ../05-grounding/index.md
[engine-ground-bus]: ../05-grounding/01-engine-bay-ground-bus.md
[power-gen]: ../01-power-generation/index.md
[aux-battery]: ../03-aux-battery-distribution/index.md
[starter]: ../../02-engine-systems/01-starter.md
[alternator]: ../01-power-generation/02-alternator.md
[radios]: ../../07-communication-systems/index.md
[circuit-breakers]: 01-circuit-breakers.md
[radiator-fan]: ../../02-engine-systems/06-radiator-fan.md
[brake-booster]: ../../02-engine-systems/02-brake-booster.md
[transmission]: ../../10-drivetrain/01-transmission.md
[ignition-signal]: ../06-ignition-signal/index.md
[constant-bus]: ../03-aux-battery-distribution/02-constant-bus.md
[standards-exceptions]: ../STANDARDS-EXCEPTIONS.md
