sob/shopmanual.io/docs/jeep_lj/01-power-systems/04-pmu/02-pmu-inputs.md

---
hide:
  - toc
---

# 1.4.2 PMU Inputs {#pmu-inputs}

PMU input configuration including digital inputs, analog inputs, CAN bus integration, and ignition signal distribution.

## 12V Switched Input (Pin 7)

**Source:** Dedicated 18 AWG wire tapped from the ignition signal bus bar (which is fed by PBS-I PINK IGN output — see [Keyless Ignition][keyless-ignition] and [Ignition Signal Distribution][ignition-signal])

**Function:** Provides switched power reference for PMU logic

**Implementation:** Dedicated wire through firewall (Grommet 2) direct to PMU Pin 7

**Load:** ~50mA

See [Ignition Signal Distribution][ignition-signal] for complete wiring architecture.

## Digital Inputs (Trigger Sources)

**Note:** Pin 7 (physical 12V switched input above) is separate from In 7 (digital input channel below). Use "Pin7" in programming for ignition sense, "In7" for headlight status.

| Input | Function | Source | Connected to Output | Notes |
| :--- | :--- | :--- | :--- | :--- |
| **In 1** | Horn Button | Steering wheel button | Out 18 (Horn) | Normally open, closes when pressed |
| **In 2** | Brake Switch | Brake pedal switch | Out 21 (Brake Lights) | Normally open, closes when pedal pressed |
| **In 3** | Reverse Signal | Turbolamik aux output (Reverse) | Out 22 (Reverse Lights) | 12V from TCU when 8HP70 in Reverse |
| **In 4** | **\[Available\]** | - | - | Available for future expansion |
| **In 5** | CT4 SW4 (High Beams) | CT4 lever push, tapped after HDP24 pin 10 | Out 23 (DRL) off, Out 12 (parking) on | 12V when high beams active; needed because the CT4 drops SW3 when SW4 is on — see [DRL & Parking][drl-parking] |
| **In 6** | **\[Available\]** | - | - | Available for future expansion |
| **In 7** | CT4 SW3 (Headlights) | CT4 lever pull | Out 23 (DRL) off, Out 12 (parking) on | 12V when headlights active, disables DRL |
| **In 8** | **\[Available\]** | - | - | Available for future expansion |
| **In 9** | A/C Request | Restomod Air control head compressor output, via trinary switch ({{ tbd(146) }} — verify kit wiring on arrival) | Out 17 (A/C Clutch) | 12V when A/C commanded and refrigerant pressure in range — see [HVAC][hvac] |

**Note:** Keyless ignition is handled entirely by the self-contained Digital Guard Dawg PBS-I module — PMU is not in the keyless logic path. See [Keyless Ignition][keyless-ignition].

[keyless-ignition]: ../../05-control-interfaces/06-keyless-ignition.md
[ignition-signal]: ../06-ignition-signal/index.md
[hvac]: ../../02-engine-systems/03-hvac.md
[drl-parking]: ../../03-lighting-systems/05-drl-parking.md
[transfer-case]: ../../10-drivetrain/02-transfer-case.md#position-sensing

## Analog Inputs

| Input | Physical Pin | Range | Function | Notes |
| :--- | :--- | :---- | :--- | :--- |
| **An 1** | Dedicated | 0-5V  | Transfer case position | NP241OR 5-position switch (resistive) via divider — drives OUT19 (4x4) and OUT24 (4LO). Divider values + thresholds pending measurement ({{ tbd(145) }}). See [Transfer Case][transfer-case] |
| **An 2-8**  | Dedicated | 0-5V  | **[Available]** | Future expansion |
| **An 9-16** | OUT17-24 | 0-20V | **[Configured as outputs]** | Dual-purpose pins - currently used as OUT17-24 |

**Current Configuration:** An 9-16 configured as outputs (OUT17-24). See [PMU Outputs][pmu-outputs] for output assignments.

**J1939 Data:** Engine oil temperature and coolant temperature are monitored via J1939 CAN bus from ECM (no analog inputs needed).

## CAN Bus Integration (J1939)

PMU24 taps into existing J1939 CAN bus as stub connection (no termination).

### Bus Topology

```text
[ECM 120Ω] ←--+--+--→ [Cummins Body Harness End 120Ω]
               |  |
               |  [PMU24 - stub tap]
               |
          [Dakota Digital - stub tap]
```

### Physical Connection

- **Tap Location:** Cummins body harness (same as Dakota Digital tap)
- **Wire Gauge:** 18-20 AWG twisted pair
- **Stub Length:** <12" from tap to PMU (keep as short as possible, ideally <6")
- **Termination:** None - bus already terminated at ECM + harness end
- **PMU Setting:** Disable internal CAN termination in software

### J1939 Data Used

| SPN | Parameter | PMU Use |
| :-----: | :--- | :--- |
| **175** | Engine Oil Temp | Oil cooler fan control (OUT 7) |
| **110** | Engine Coolant Temp | PS cooler fan control (OUT 8)  |
| **190** | Engine Speed (RPM)  | Data logging |
| **100** | Engine Oil Pressure | Data logging |

See [PMU Programming][pmu-programming] for CAN-based logic examples.

## Ignition Signal Distribution

**PMU Pin 7:** 18 AWG wire tapped from the engine-bay distribution off HDP24 Pin 12 (which crosses the firewall from the ignition signal bus bar, fed by PBS-I PINK IGN)

**Routing:** Engine bay (firewall Pin 12 junction → PMU Pin 7)

**Purpose:** Shares the same switched supply path as the Cummins ECM 12V — both energize whenever the PBS-I asserts PINK IGN.

**Non-critical devices** (CT4, SwitchPros, radio, BCDC, camera) tap directly off the cabin-mounted ignition signal bus bar - see [Ignition Signal][ignition-signal] for details.

## Related Documentation

- [PMU Overview][pmu-overview] - Product specifications and capacity
- [PMU Outputs][pmu-outputs] - Output configuration and load details
- [PMU Programming][pmu-programming] - Logic examples using inputs and CAN data
- [Firewall Ingress][firewall-ingress] - Grommet 2 routing
- [Gauge Cluster][gauge-cluster] - Dakota Digital J1939 integration

[pmu-overview]: 01-pmu-overview.md
[pmu-outputs]: 03-pmu-outputs.md
[pmu-programming]: 04-pmu-programming.md
[firewall-ingress]: ../07-wire-routing/02-firewall-ingress.md
[gauge-cluster]: ../../02-engine-systems/09-gauge-cluster/index.md
[ignition-signal]: ../06-ignition-signal/index.md
