sob/shopmanual.io/docs/jeep_lj/01-power-systems/01-power-generation/03-bcdc.md

---
hide:
  - toc
tags:
  - product-details
  - power-generation
  - battery-charger
  - dc-dc-charger
---

# 1.1.3 BCDC Alpha 50 {#bcdc-alpha-50}

/// html | div.product-info
RedArc BCDC Alpha 50

**Type:** Battery Isolator and DC-DC Charger

**Model:** RedArc BCDC Alpha 50 (BCDC1250R)

**Manufacturer:** RedArc Electronics

**Product Page:** [BCDC Alpha 50][redarc-bcdc]

**Installation Guide:** [BCDC Alpha Installation Manual][bcdc-install]

**Instruction Manual:** [BCDC Alpha Instruction Manual][bcdc-manual]

///

## Specifications

- **Output:** 50A DC-DC charging, multi-stage LiFePO4/AGM compatible (0.37C charge rate for 135Ah LiFePO4)
- **Inputs:** 9-32V primary (alternator), 9-48V solar (up to 350W)
- **Features:** Auto isolation, jump start assist, Green Power Priority, ignition-triggered
- **Dimensions:** 260mm L × 160mm W × 70mm H
- **Full Specs:** [Installation Manual][bcdc-install] | [Instruction Manual][bcdc-manual]

## Wiring

| Connection | Terminal Label | Terminal Size | Source/Destination | Notes |
| :--- | :--- | :--- | :--- | :--- |
| Start Battery (+) | Red | M5[^bcdc-terminals] | START battery positive | See [START Battery Distribution][starter-battery] for wire specs |
| Auxiliary Battery (+) | Brown | M5[^bcdc-terminals] | AUX battery positive | See [AUX Battery Distribution][aux-battery] for wire specs |
| Solar (+) | Yellow | M5[^bcdc-terminals] | Cascadia 4x4 80W panel | M5 lug on 10 AWG - see [Solar Charging][solar] |
| Ground (-) | Black | M5[^bcdc-terminals] | AUX battery negative | See [AUX Battery Distribution][aux-battery] for wire specs |
| Ignition | Blue | Spade | PMU ignition sense tap | 18 AWG - see [PMU Inputs][pmu-inputs] |
| Battery Temp Sensor | +/- (reversible) | 2-pin plug | AUX battery positive terminal | **REQUIRED** - LiFePO4 temperature-compensated charging |

[^bcdc-terminals]: RedArc *BCDC Alpha 50R Installation Guide* (INST185-2), terminal-connection section: "For the Ground, Auxiliary, Start Battery and Solar terminals, use M5 lugs or equivalent, with a barrel size to suit the required cable gauge." Screws are supplied with the unit (M5×10mm for these four terminals; M3×8mm for ignition); a maximum of two lugs may be connected per main-unit terminal. Supersedes the earlier unsourced M8 figure listed for the Red/Brown/Black terminals.

See [START Battery Distribution][starter-battery] and [AUX Battery Distribution][aux-battery] for complete wire specifications (gauge, distance, routing, circuit breakers).

**Critical:** Verify solar input polarity before connection - reverse polarity damages unit.

[starter-battery]: ../02-starter-battery-distribution/index.md
[aux-battery]: ../03-aux-battery-distribution/index.md

## Function

The BCDC manages charging and isolation between starter and aux batteries:

- **Normal Operation:** Charges AUX battery from START battery/alternator at up to 50A
- **Solar Priority:** Uses solar input first when available (Green Power Priority)
- **Jump Start Assist:** Parallels batteries if START battery voltage drops critically
- **Isolation:** Prevents AUX battery from draining START battery when engine off

## AUX Battery Charging Impact

**Upgrade from 25A to 50A BCDC provides significant improvement for high-draw scenarios:**

| Scenario | AUX Draw | 25A BCDC | 50A BCDC | Improvement |
| :--- | :--- | :--- | :--- | :--- |
| Night Offroad (full lights) | 70A | -45A drain | **-20A drain** | 2.3× longer runtime |
| Airing Up Tires | 110A | -85A drain | **-60A drain** | 30% less battery impact |
| Recovery after air-up | - | 34 min to recover 10Ah | **17 min** | Half the recovery time  |

See [AUX Battery Load Analysis][aux-load-analysis] for complete scenario details.

## Mounting

- **Location:** Passenger rear wheel well near AUX battery (water-protected, accessible for LED visibility)
- **Installation:** See [Section 1 Installation Checklist][installation-checklist]

## Temperature Sensor Installation

**REQUIRED** for AGM charge compensation - NTC thermistor, 2-pin reversible, ~6 ft cable (included with BCDC).

- **Mount:** Ring terminal under the AUX battery positive terminal bolt - reads both voltage and temperature at the battery.

[redarc-bcdc]: https://www.redarcelectronics.com/products/the-manager30
[bcdc-install]: https://cdn.intelligencebank.com/au/share/yE9N/zJpl/NNRlJ/original/Install+Guide+BCDC+Alpha+50R+EN
[bcdc-manual]: https://cdn.intelligencebank.com/au/share/yE9N/zJpl/l7ZzG/original/Instruction+Manual+BCDC+Alpha+50R+EN
[solar]: 04-solar.md
[pmu-inputs]: ../04-pmu/02-pmu-inputs.md
[installation-checklist]: ../../09-installation/01-power-systems-checklist.md#phase-2-power-distribution
[aux-load-analysis]: ../08-load-analysis/03-aux-battery.md
