sob/shopmanual.io/docs/jeep_lj/01-power-systems/03-aux-battery-distribution/04-safetyhub.md

---
hide:
  - toc
tags:
  - product-details
  - power-distribution
  - fuse-block
---

# 1.3.4 SafetyHub 150 (AUX Battery) {#aux-safetyhub-150}

/// html | div.product-info
Blue Sea SafetyHub 150

**Type:** Fuse Block

**Model:** Blue Sea 7748 SafetyHub 150

**Manufacturer:** Blue Sea Systems

**Product Page:** [SafetyHub 150 Fuse Block][bluesea-7748]

///

## Overview

Provides fused distribution for recovery and auxiliary systems powered by the AUX battery.

**Location:** Passenger rear wheel well (co-located with AUX battery and circuit breakers)

**Power Source:** AUX battery+ via inline 150A CB (~2 ft, local in rear wheel well) - see [Circuit Breakers][circuit-breakers]

**Note:** Communications systems (GMRS, Intercom) are powered via PMU outputs - see [PMU Outputs][pmu-outputs]

!!! note "Future-Proof Capacity"
Wire and CB sized for full 150A SafetyHub capacity (current load 90A). Provides 60A headroom for additional recovery or auxiliary systems.

## Specifications

- **Rating:** 150A max combined (400A bus rating)
- **Fuse Types:** 3x MIDI (AMI/MIDI), 4x ATC (ATO/ATC)
- **Fuse Range:** MIDI: 30-200A, ATC: 1-20A per circuit
- **Features:** Ignition protected, negative ground bus, ISO 8846, SAE J1171, IP66
- **Full Specs:** [Blue Sea 7748][bluesea-7748]

## Circuit Configuration

| Slot | Fuse | Circuit | Wire Gauge | Distance | Voltage @ Load | Load | Notes |
| :----- | :--- | :--- | :--- | :--- | :--- | :--- | :--- |
| MIDI-1 | 60A  | [ARB Compressor][air-system] Motor 1 | 6 AWG ✓ | ~12 ft {{ tbd(154) }} | 11.56V (3.6%)  | 45A  | Passenger rear wheel well → cargo → under passenger seat |
| MIDI-2 | 60A  | [ARB Compressor][air-system] Motor 2 | 6 AWG ✓ | ~12 ft {{ tbd(154) }} | 11.56V (3.6%)  | 45A  | Passenger rear wheel well → cargo → under passenger seat |
| MIDI-3 | - | **\[Available\]** | - | - | - | - | - |
| ATC-1  | - | **\[Available\]** | - | - | - | - | (Was Winch Contactor Trigger - reallocated 2026-05-30 to BODY PDU CB43 for shorter routing; see [Winch][recovery-systems] and [Dashboard Controls][dashboard-controls]) |
| ATC-2  | - | **\[Available\]** | - | - | - | - | - |
| ATC-3  | - | **\[Available\]** | - | - | - | - | - |
| ATC-4  | - | **\[Available\]** | - | - | - | - | - |

**Slot Utilization:** 2 of 7 used (2 MIDI, 5 available — ATC-1 freed after winch trigger reallocated to BODY PDU CB43)

**Total Load:** 90A maximum (ARB only — winch control reallocated to BODY PDU CB43)

**Utilization:** 90A / 150A = 60%

**Future Capacity:** 60A additional capacity available (150A max - 90A current = 60A headroom)

!!! info "Winch Main Power"
Winch motor power (409A peak) connects directly to AUX battery positive terminal with no external circuit breaker per WARN manufacturer specifications. See [STANDARDS-EXCEPTIONS.md][standards-exceptions] and [Recovery Systems][recovery-systems] for complete protection strategy.

## Related Documentation

**Power Systems:**

- [AUX Battery Distribution Overview][aux-battery]
- [Circuit Breakers][circuit-breakers] - 150A CB protection
- [PMU Outputs][pmu-outputs] - Communications system power (GMRS, Intercom)
- [Standards Exceptions][standards-exceptions] - Winch protection strategy documentation

**Connected Systems:**

- [Air System][air-system] - ARB twin compressor specifications
- [Recovery Systems][recovery-systems] - Winch control and protection details

[bluesea-7748]: https://www.bluesea.com/products/7748/SafetyHub_150_Fuse_Block
[circuit-breakers]: 01-circuit-breakers.md
[air-system]: ../../08-exterior-systems/02-air-compressor.md
[recovery-systems]: ../../08-exterior-systems/01-winch.md
[aux-battery]: index.md
[pmu-outputs]: ../04-pmu/03-pmu-outputs.md
[standards-exceptions]: ../STANDARDS-EXCEPTIONS.md
[dashboard-controls]: ../../05-control-interfaces/05-dashboard-controls.md
