sob/shopmanual.io/docs/jeep_lj/02-engine-systems/09-gauge-cluster/05-bim-tpms.md

---
hide:
  - toc
tags:
  - product-details
  - gauge-cluster
  - bim-module
  - tpms
---

# 2.9.5 BIM-22-3 (Tire Pressure Monitoring System) {#bim-tpms-module}

/// html | div.product-info
Dakota Digital BIM-22-3 TPMS

**Type:** Tire Pressure Monitoring System (TPMS)

**Model:** BIM-22-3

**Manufacturer:** Dakota Digital

**Product Page:** [Tire Pressure Monitoring System][product-link]

**Manual:** [BIM-22-3 Manual][manual-link]

///
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
