sob/shopmanual.io/export/Jeep LJ Dash Layout-Console---front-plate.png

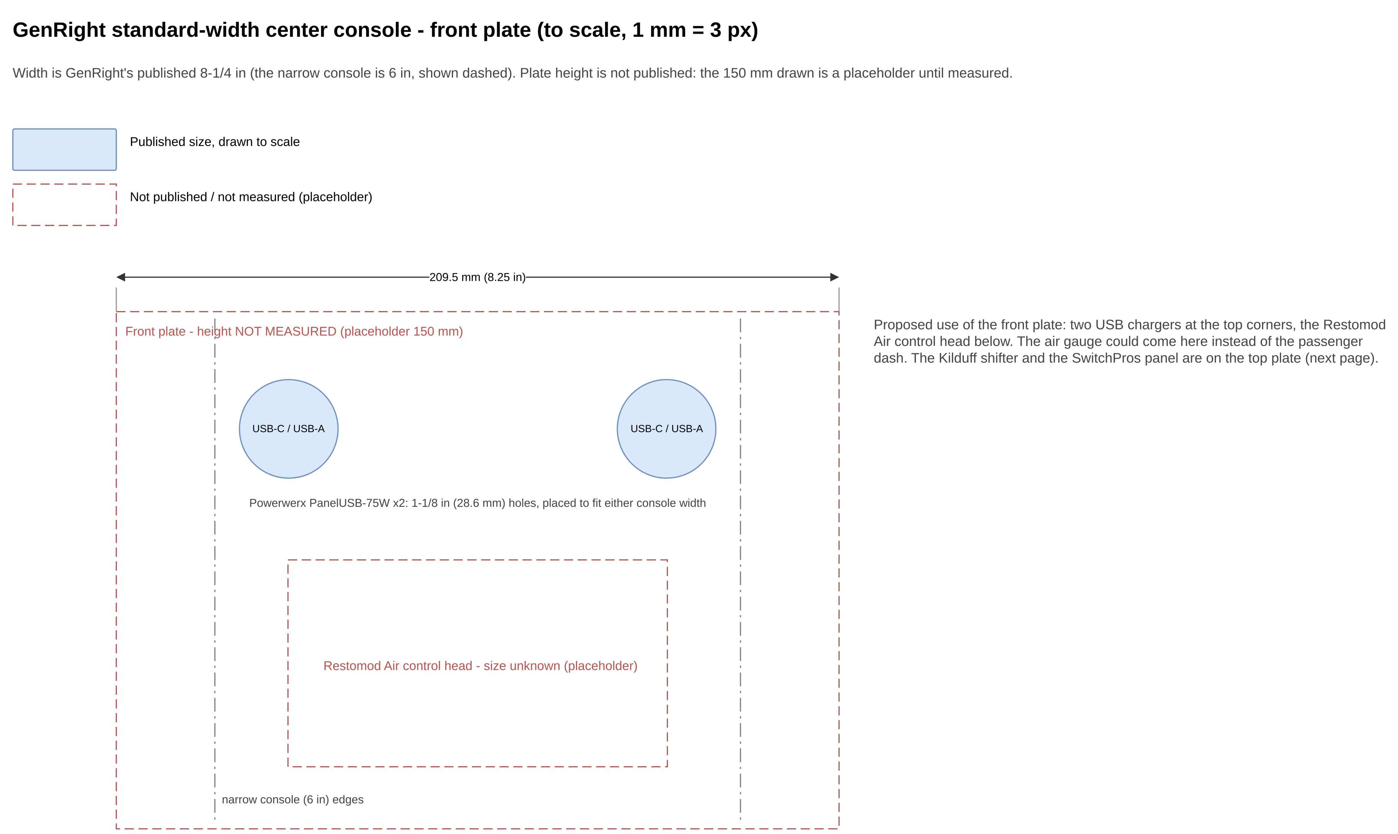
export/Jeep LJ Dash Layout-Console---front-plate.png
