sob/shopmanual.io/export/Jeep LJ Dash Layout-Console---top-plate.png

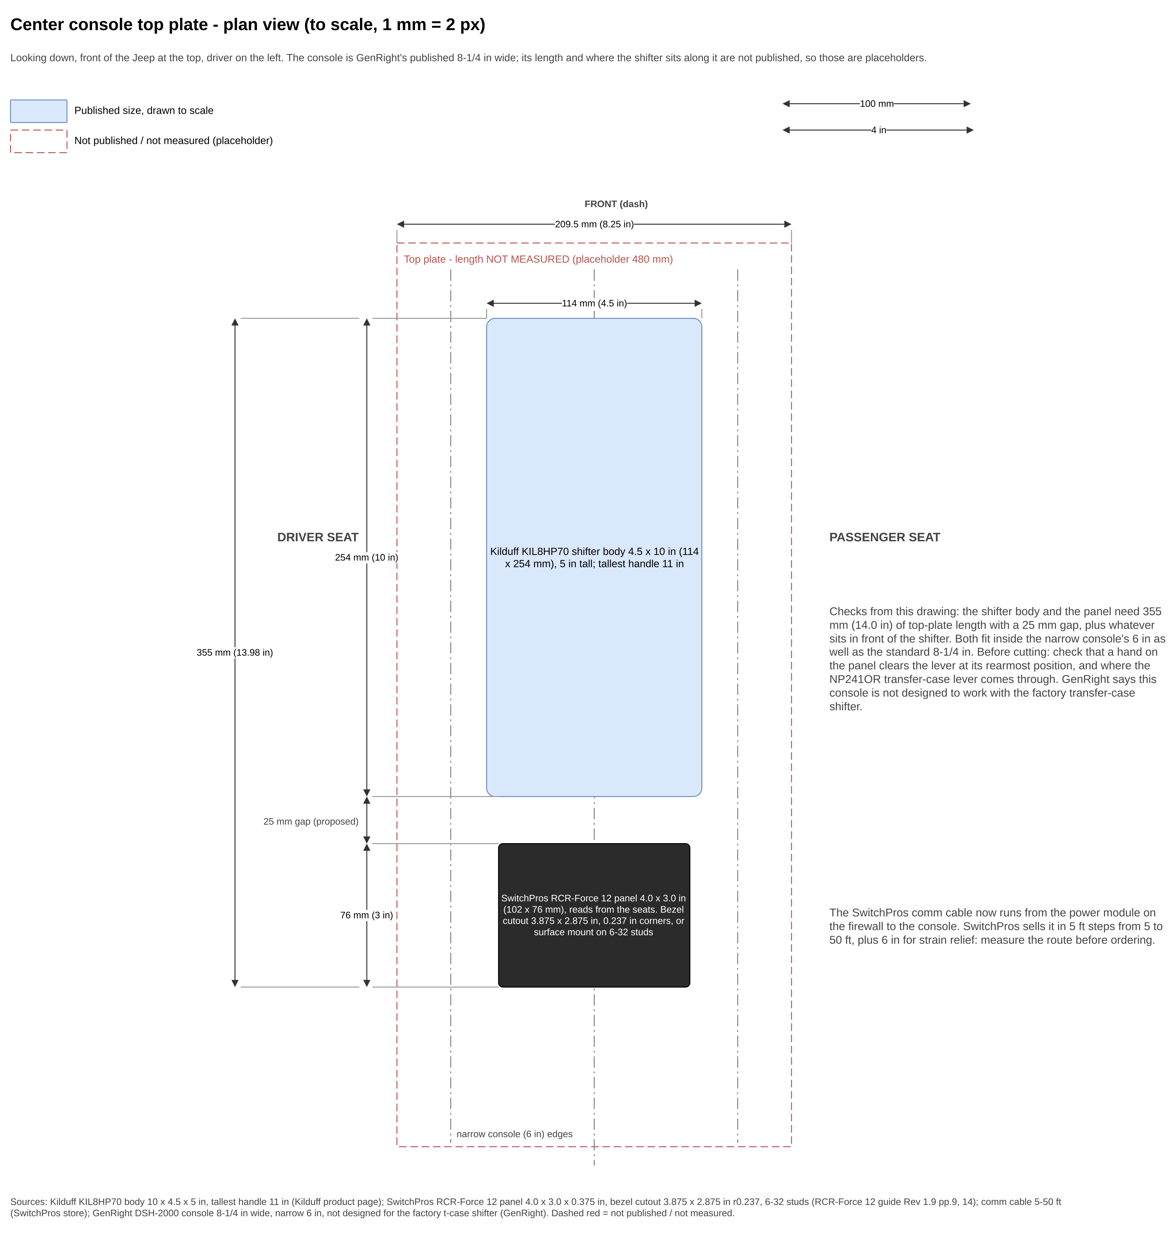
export/Jeep LJ Dash Layout-Console---top-plate.png
