sob/shopmanual.io/export/Jeep LJ Dash Layout-Dash---driver-view.png

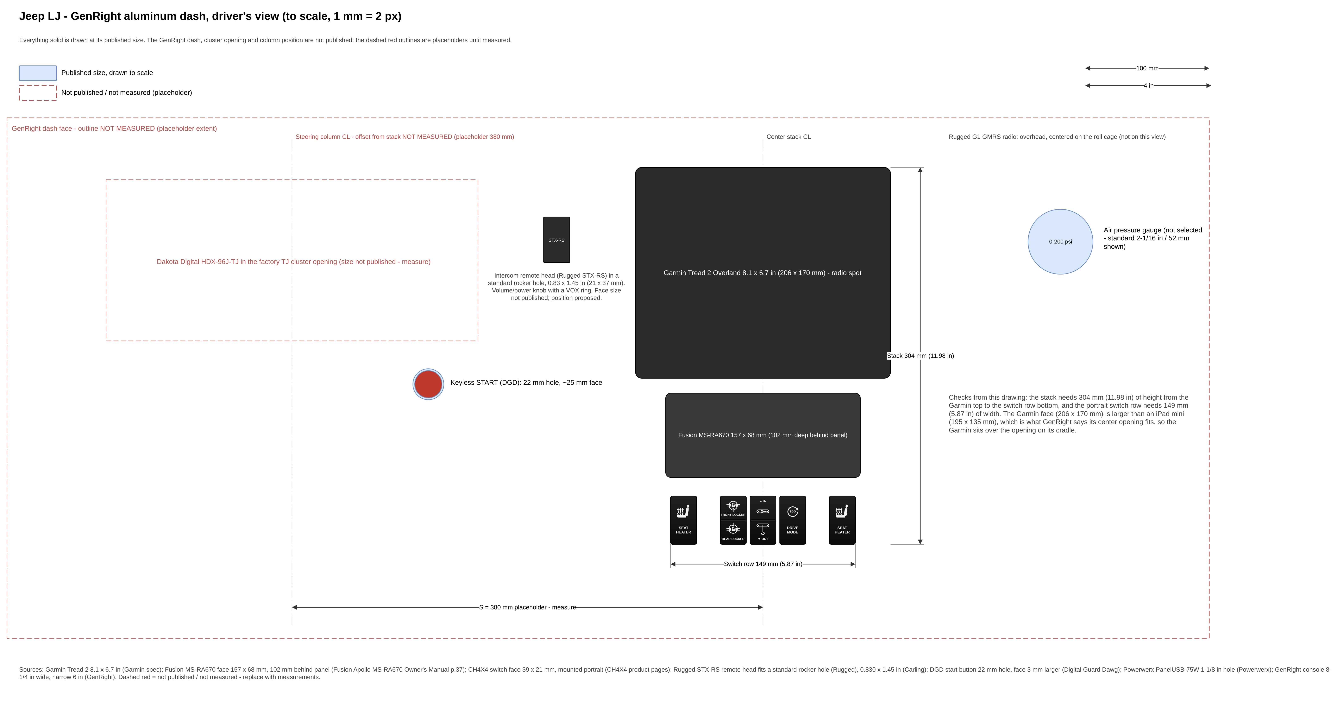
export/Jeep LJ Dash Layout-Dash---driver-view.png
