sob/shopmanual.io/export/Jeep LJ Dash Layout-Switch-row---detail.png

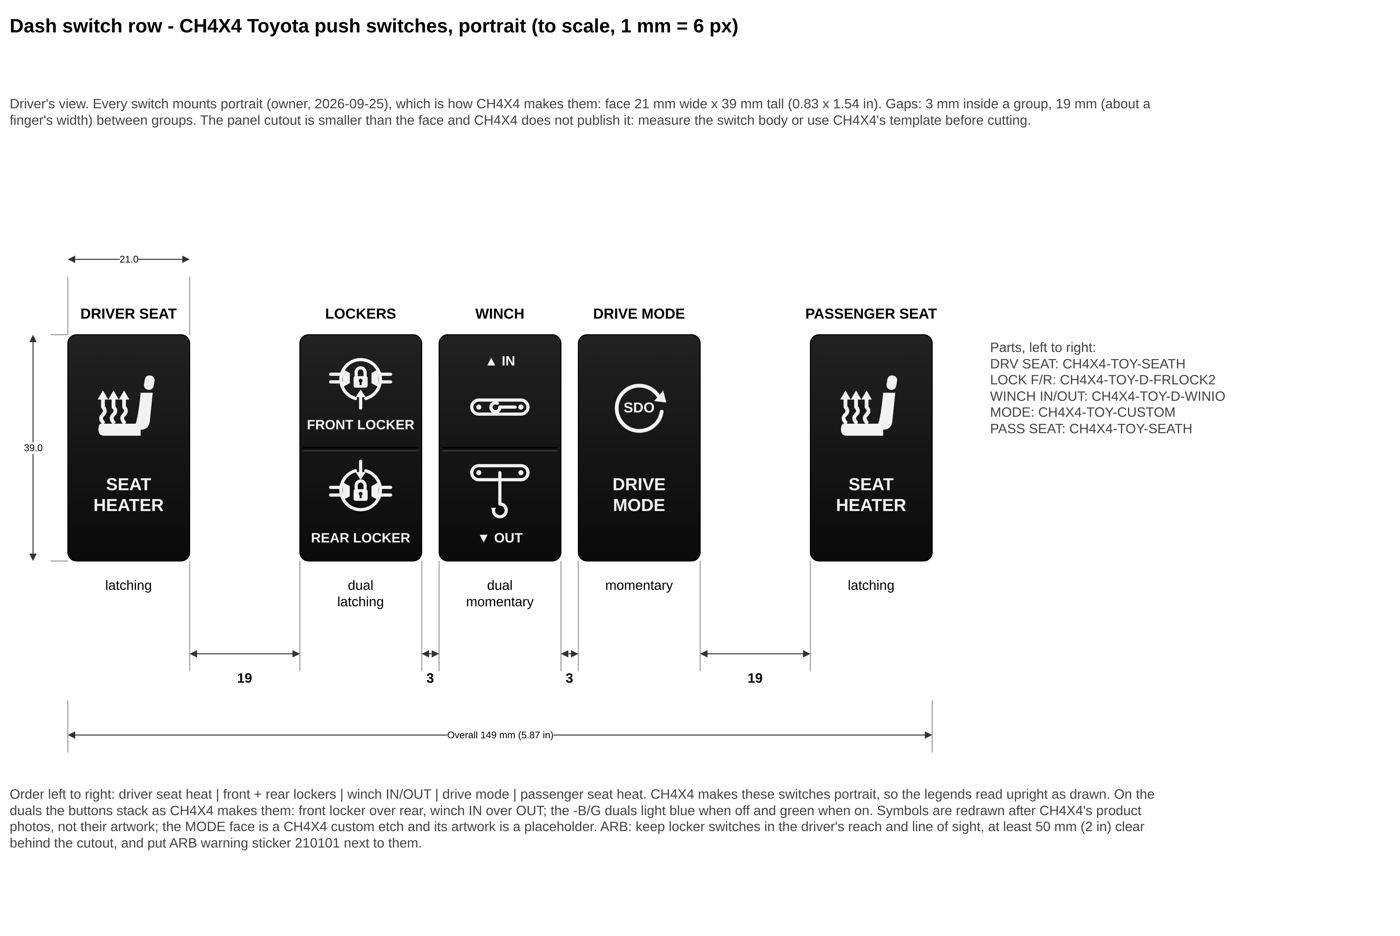
export/Jeep LJ Dash Layout-Switch-row---detail.png
