sob/shopmanual.io/export/Van Electrical-As-Built.png

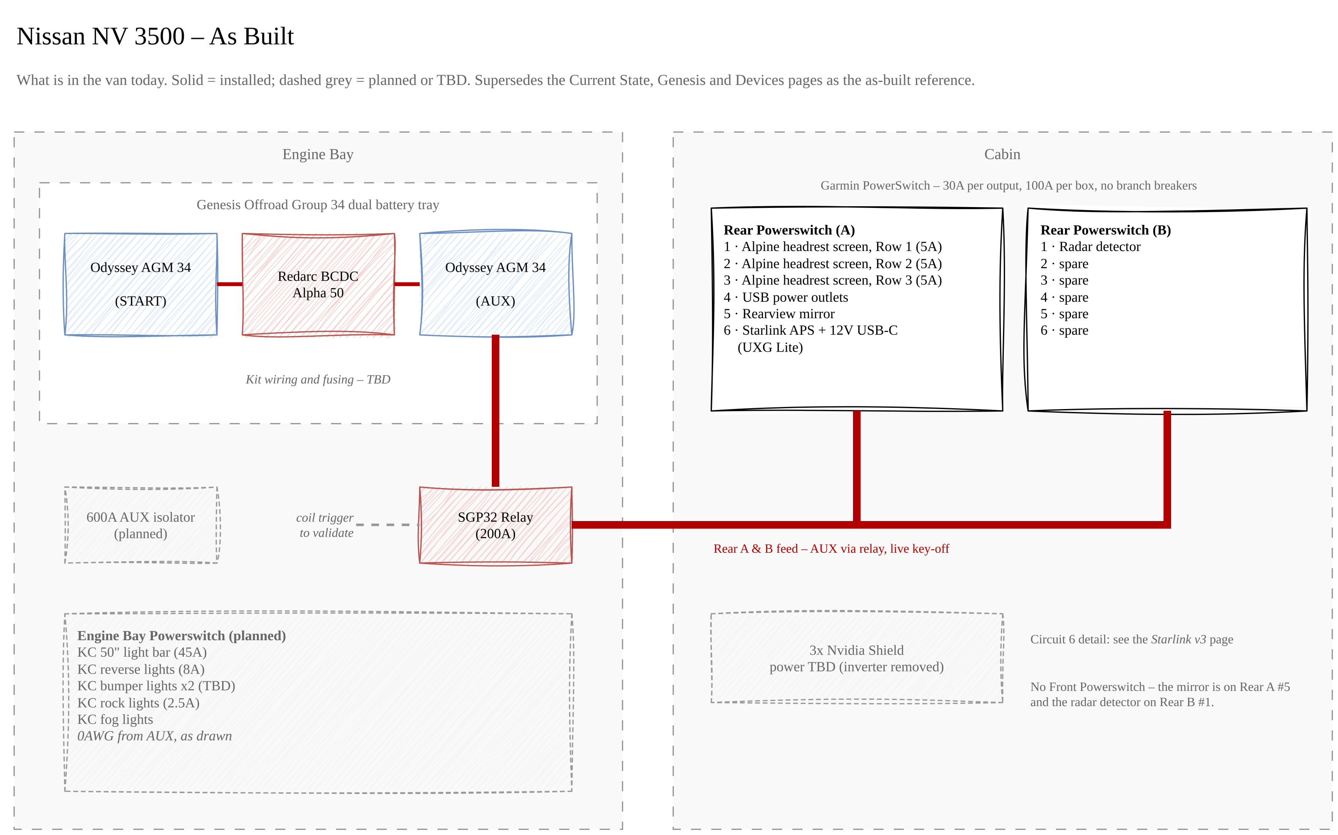
export/Van Electrical-As-Built.png
