sob/shopmanual.io/export/Van Electrical-Starlink-v2.png

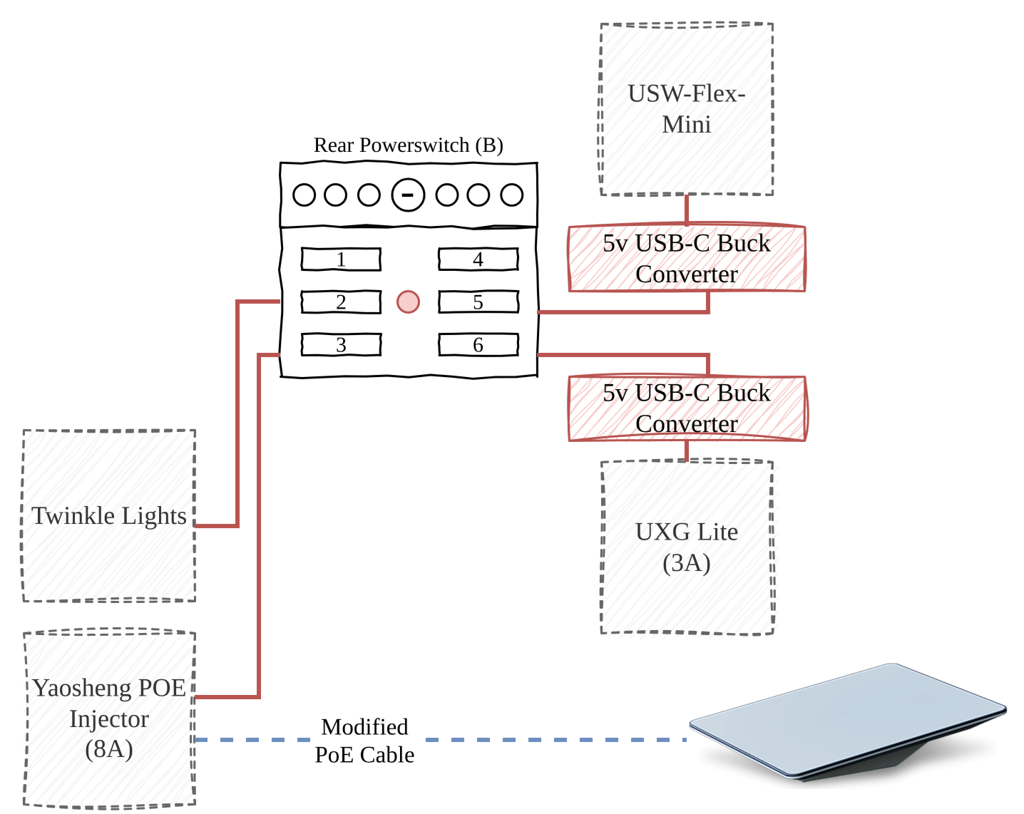
export/Van Electrical-Starlink-v2.png
